rvwagner/TychoRover/web/images/OverlaySpin.png

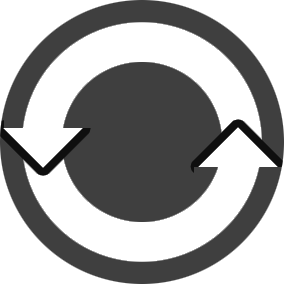
web/images/OverlaySpin.png
