rvwagner/TychoRover/scripts/tycho_logger.py

#!/usr/bin/python3

import rospy
from tycho.msg import WheelAnglesSpeeds
from tycho.msg import WheelStatus
from tycho.msg import RoverDriveCommand
from tycho.msg import PowerMonitor
from sensor_msgs.msg import Joy
from std_msgs.msg import Float32MultiArray
from std_msgs.msg import Int16
from sensor_msgs.msg import Joy


#########
# SETUP #
#########


class JoyLogger:
    def __init__(self, directory):
        rospy.Subscriber("tycho/joy", Joy, self.log, queue_size=100)
        self.file = open("%s/joystick_log.txt"%directory, 'w', buffering=1)
        self.file.write("date, x_axis, y_axis, buttons 1, 2, 3, 4, 5, 6")
    #
    
    def closeout(self):
        self.file.close()
    #
    
    def add_flag(self, id):
        t = datetime.datetime.today().strftime("%Y-%m-%d %H:%M:%S.%f")
        self.file.write("%s  FLAGGED EVENT %d\n"%(t,id))
    #
    
    def log(self, msg):
        dt = datetime.datetime.fromtimestamp(msg.header.stamp.to_time())
        timestamp = dt.strftime("%Y-%m-%d %H:%M:%S.%f")
        self.file.write("%s  X=% 6.4f Y=% 6.4f ; Buttons = %d %d %d %d %d %d\n"%(timestamp, msg.axes[0], msg.axes[1], msg.buttons[0], msg.buttons[1], msg.buttons[2], msg.buttons[3], msg.buttons[4], msg.buttons[5]))
    #
#

class PowerMonitorLogger:
    def __init__(self, directory):
        rospy.Subscriber("/tycho/power_monitor", PowerMonitor, self.log, queue_size=100)
        self.file = open("%s/console_power_log.txt"%directory, 'w', buffering=1)
        self.file.write("date, Battery_1_V, Battery_2_V, Battery_3_V, Battery_4_V, 12V_V, 5V_V, Master_A, Front_Relay_A, Rear_Relay_A, Display_A, 12V_A, 5V_A")
    #
    
    def closeout(self):
        self.file.close()
    #
    
    def add_flag(self, id):
        t = datetime.datetime.today().strftime("%Y-%m-%d %H:%M:%S.%f")
        self.file.write("%s  FLAGGED EVENT %d\n"%(t,id))
    #
    
    def log(self, msg):
        dt = datetime.datetime.fromtimestamp(msg.header.stamp.to_time())
        timestamp = dt.strftime("%Y-%m-%d %H:%M:%S.%f")
        self.file.write("%s, %5.2f, %5.2f, %5.2f, %5.2f, %5.2f, %5.2f, %5.2f, %5.2f, %5.2f, %5.2f, %5.2f, %5.2f\n"%(timestamp, msg.battery_1_v, msg.battery_2_v, msg.battery_3_v, msg.battery_4_v, msg.panel_12v_v, msg.panel_5v_v, msg.master_a, msg.front_relay_a, msg.rear_relay_a, msg.panel_display_a, msg.panel_12v_a, msg.panel_5v_a))
    #
#


class RoverDriveCommandLogger:
    def __init__(self, directory):
        rospy.Subscriber("/tycho/final_commands", RoverDriveCommand, self.log, queue_size=100)
        self.file = open("%s/high_level_command_log.txt"%directory, 'w', buffering=1)
        self.file.write("date, speed, turn_center_x, turn_center_y, strafing_angle, is_strafing, is_braking\n")
    #
    
    def closeout(self):
        self.file.close()
    #
    
    def add_flag(self, id):
        t = datetime.datetime.today().strftime("%Y-%m-%d %H:%M:%S.%f")
        self.file.write("%s  FLAGGED EVENT %d\n"%(t,id))
    #
    
    def log(self, msg):
        dt = datetime.datetime.fromtimestamp(msg.header.stamp.to_time())
        timestamp = dt.strftime("%Y-%m-%d %H:%M:%S.%f")
        self.file.write("%s  % 6.2f % 6.2f % 6.2f % 6.2f %d %d\n"%(timestamp, msg.speed, msg.turn_center_x, msg.turn_center_y, msg.strafing_angle, msg.is_strafing, msg.is_braking))
    #
#

class WheelAnglesSpeedsLogger:
    def __init__(self, directory):
        rospy.Subscriber("tycho/low_level_motor_values", WheelAnglesSpeeds, self.log, queue_size=100)
        self.file = open("%s/low_level_command_log.txt"%directory, 'w', buffering=1)
        self.file.write("date, front_left_angle, front_left_speed, front_right_angle, front_right_speed, back_left_angle, back_left_speed, back_right_angle, back_right_speed")
    #
    
    def closeout(self):
        self.file.close()
    #
    
    def add_flag(self, id):
        t = datetime.datetime.today().strftime("%Y-%m-%d %H:%M:%S.%f")
        self.file.write("%s  FLAGGED EVENT %d\n"%(t,id))
    #
    
    def log(self, msg):
        dt = datetime.datetime.fromtimestamp(msg.header.stamp.to_time())
        timestamp = dt.strftime("%Y-%m-%d %H:%M:%S.%f")
        self.file.write("%s  % 6.2f % 6.2f % 6.2f % 6.2f % 6.2f % 6.2f % 6.2f % 6.2f\n"%(timestamp, msg.front_left_angle, msg.front_left_speed, msg.front_right_angle, msg.front_right_speed, msg.back_left_angle, msg.back_left_speed, msg.back_right_angle, msg.back_right_speed))
    #
#


class WheelStatusLogger:
    def __init__(self, directory):
        rospy.Subscriber("tycho/wheel_status", WheelStatus, self.log, queue_size=100)
        # open files for writing
        self.nodefilelist = []
        self.nodefilelist.append(open("%s/node_1_responses_log.txt"%directory, 'w', buffering=1))
        self.nodefilelist.append(open("%s/node_2_responses_log.txt"%directory, 'w', buffering=1))
        self.nodefilelist.append(open("%s/node_3_responses_log.txt"%directory, 'w', buffering=1))
        self.nodefilelist.append(open("%s/node_4_responses_log.txt"%directory, 'w', buffering=1))
        
        for node in [0, 1, 2, 3]:
            self.nodefilelist[node].write("Date   DRIVE: FF & FS & MOTCMD_2 -> Final_Drive_Speed = MOTPWR_Drive     ; Steer: t Target_Steering_Angle = m Target_Steering_Power ? cmd MOTPWR_Steer act Current_Steering_Angle")
            self.nodefilelist[node].write("FF: Page 245    FS: page 247")
    #
    
    def closeout(self):
        #Close all files
        self.nodefilelist[0].close()
        self.nodefilelist[1].close()
        self.nodefilelist[2].close()
        self.nodefilelist[3].close()
    #
    
    def add_flag(self, id):
        t = datetime.datetime.today().strftime("%Y-%m-%d %H:%M:%S.%f")
        for node in [0, 1, 2, 3]:
            self.nodefilelist[node].write("%s  FLAGGED EVENT %d\n"%(t,id))
    #
    
    def log(self, msg):
        node=msg.wheel_id
        dt = datetime.datetime.fromtimestamp(msg.header.stamp.to_time())
        timestamp = dt.strftime("%Y-%m-%d %H:%M:%S.%f")
        # Drive/steer coord debugging data
        #self.nodefilelist[node-1].write("%s  Node %d: Drive: %08X -> % 6.0f = % 6.0f; Steer: t % 6.0f = m % 6.0f ? cmd % 6.0f act % 6.0f\n"%(timestamp, node, int(msg.drive_rpm), msg.drive_amps, msg.drive_spin_count, msg.controller_temp, msg.steering_temp, msg.steering_amps, msg.drive_temp))
        self.nodefilelist[node-1].write("%s  Node %d: D: % 6.1f mm/s  % 6.1f A  % 8d ticks  % 6.1f drg  S: % 6.1f A  % 6.1f C  MC: % 6.1f C Flags ...\n"%(timestamp, node, msg.drive_rpm, msg.drive_amps, msg.drive_spin_count, msg.drive_temp, msg.steering_amps, msg.steering_angle, msg.controller_temp))
        if node == 2: #print("Node %d: Drive: %08X -> % 6.0f = % 6.0f; Steer: t % 6.0f = m % 6.0f ? cmd % 6.0f act % 6.0f\n"%(node, int(msg.drive_rpm), msg.drive_amps, msg.drive_spin_count, msg.controller_temp, msg.steering_temp, msg.steering_amps, msg.drive_temp))
            print("%s  Node %d: D: % 6.1f mm/s  % 6.1f A  % 8d ticks  % 6.1f C  S: % 6.1f A  % 6.1f deg  MC: % 6.1f C Flags ...\n"%(timestamp, node, msg.drive_rpm, msg.drive_amps, msg.drive_spin_count, msg.drive_temp, msg.steering_amps, msg.steering_angle, msg.controller_temp))
    #
#

#############
# Main Loop #
#############

import datetime
import os
import errno

t = datetime.datetime.today()

# Set up log directory
# ~/tycho_logs/{date}_{time}
logdir = t.strftime("/home/pi/tycho_logs/%Y%m%d_%H%M%S")
os.makedirs(logdir, exist_ok=True)
try:
    os.symlink(logdir, "/home/pi/tycho_logs/latest")
except OSError as e:
    if e.errno == errno.EEXIST:
        os.remove("/home/pi/tycho_logs/latest")
        os.symlink(logdir, "/home/pi/tycho_logs/latest")
    else:
        raise e
#
print ("Created log directory '%s'"%logdir)


# starts the node
rospy.init_node('Logger')

# Set up logging objects
print("Subscribing to topics")
wsl = WheelStatusLogger(logdir)
rdcl = RoverDriveCommandLogger(logdir)
wasl = WheelAnglesSpeedsLogger(logdir)
jl = JoyLogger(logdir)
pml = PowerMonitorLogger(logdir)

event_id = 1;
def add_flag(msg):
    global event_id
    wsl.add_flag(event_id)
    rdcl.add_flag(event_id)
    wasl.add_flag(event_id)
    jl.add_flag(event_id)
    pml.add_flag(event_id)
    print("FLAG EVENT %d"%event_id)
    event_id += 1
#

rospy.Subscriber("tycho/log_flag", Int16, add_flag, queue_size=1)

print ("Starting main loop")
rate = rospy.Rate(1) # Hz
while not rospy.is_shutdown():
    rate.sleep()
#

wsl.closeout()
rdcl.closeout()
wasl.closeout()
jl.closeout()
pml.closeout()
